wyolum/TiNA/KiCAD/TiNA_Images/TiNA_Images.pdf

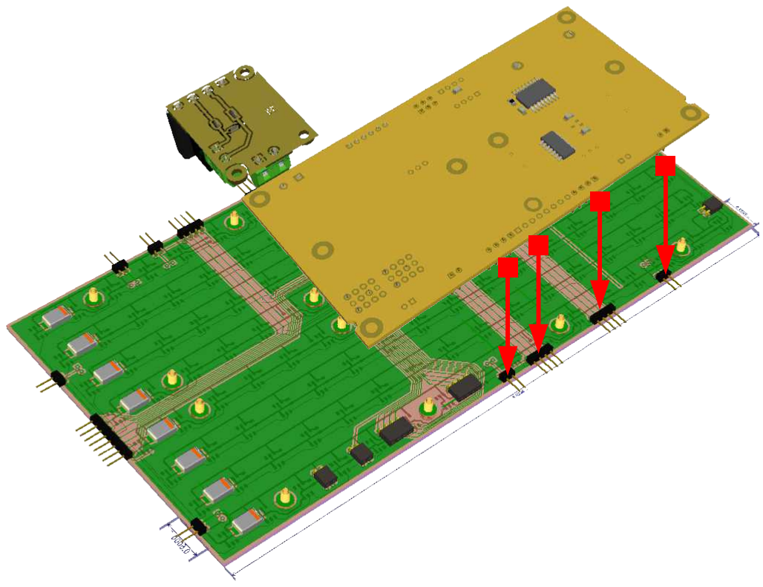
[picture p3: figure]

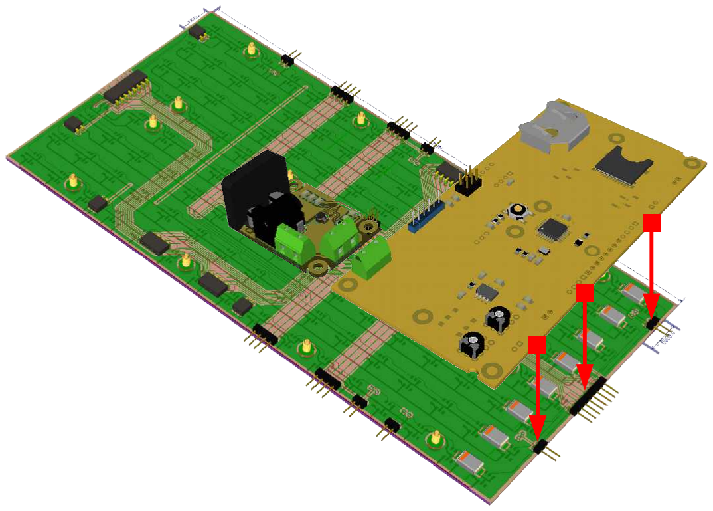
[picture p4: figure]

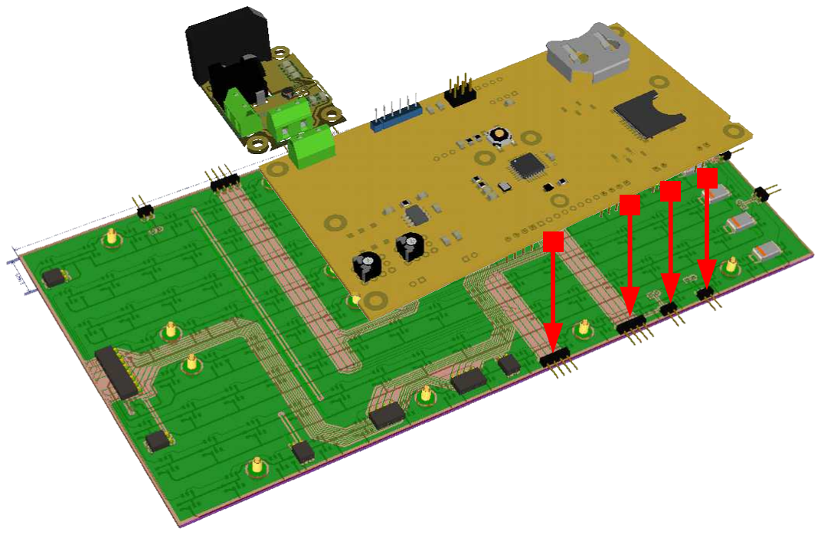
[picture p5: figure]
