wyolum/TiNA/KiCAD/TiNA_Images/TiM_01.png

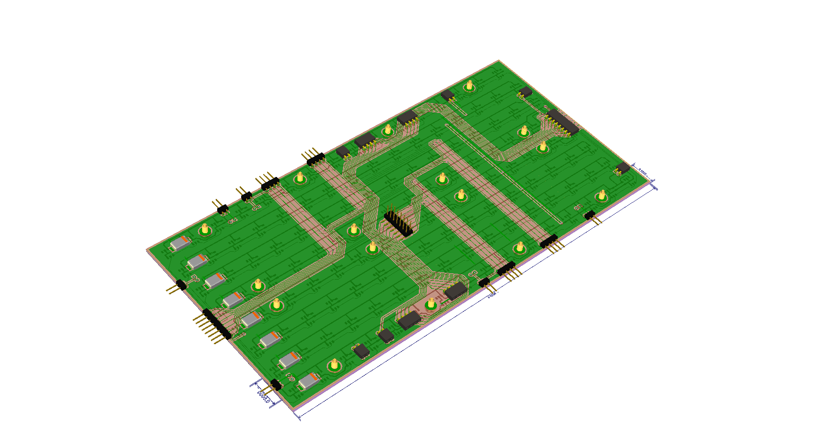
KiCAD/TiNA_Images/TiM_01.png
