wyolum/TiNA/KiCAD/TiNA_Images/TiM_02.png

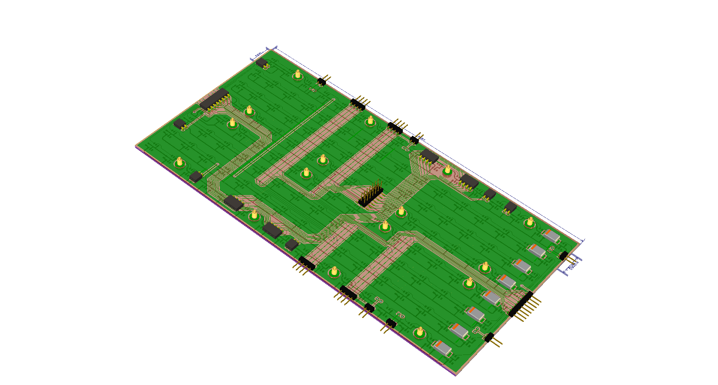
KiCAD/TiNA_Images/TiM_02.png
