wyolum/TiNA/KiCAD/TiNA_Images/TiM_03.png

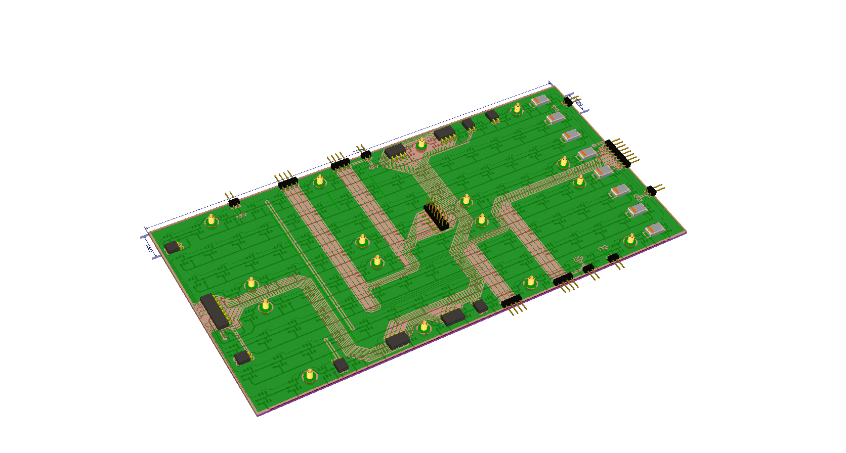
KiCAD/TiNA_Images/TiM_03.png
