wyolum/TiNA/KiCAD/TiNA_Images/TiNA_03.png

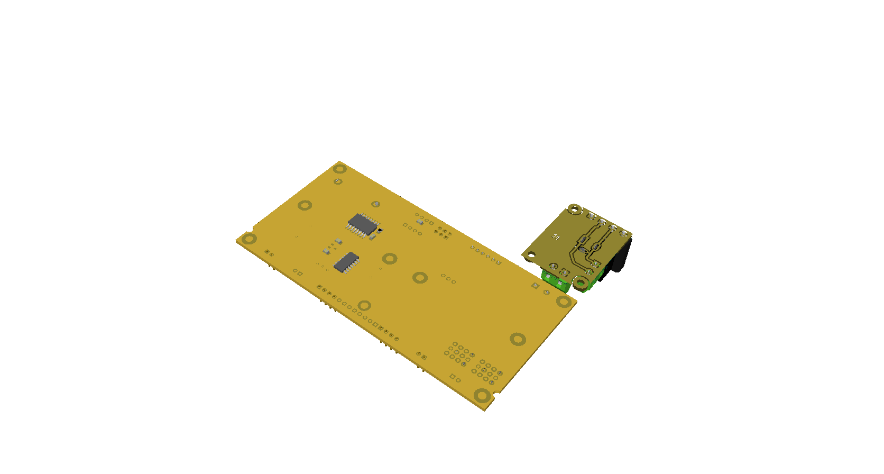
KiCAD/TiNA_Images/TiNA_03.png
