wyolum/TiNA/KiCAD/TiNA_Images/TiNA_04.png

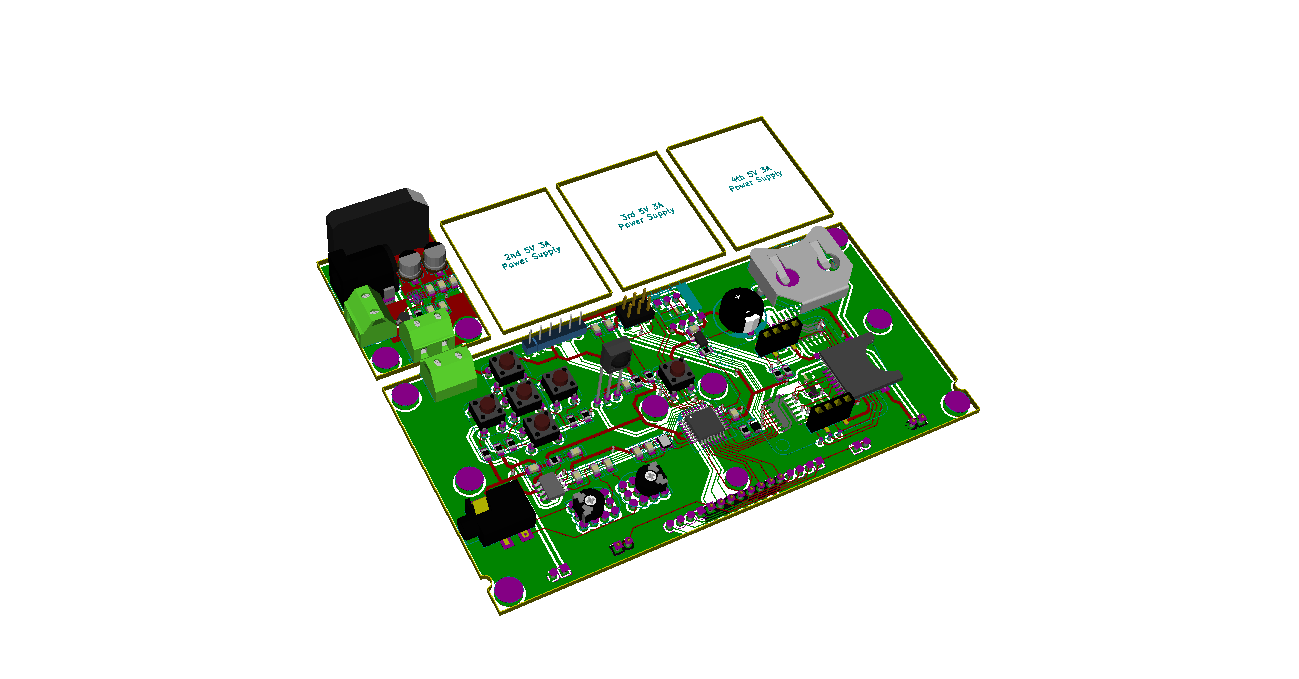
KiCAD/TiNA_Images/TiNA_04.png
